aiurat-and-ilya/hv-test-stand/electronics/simulation/hv-test-stand-sim.cir

[Main]
FileType=CIR
Version=12.00
Program=Micro-Cap
Component Version=10.00
Shape Version=11.00
Screen=1920,1080
MCAPVersion=12.2.0.5
Key ID=Demo
NLCnt=221
TXCnt=0

[shapedef]
Name=a_dip8
Block=0,-24,56,40,0,8
BlockLine="Line",-16,-16
BlockLine="Line",-16,0
BlockLine="Line",-16,16
BlockLine="Line",-16,32
BlockLine="Line",72,-16
BlockLine="Line",72,0
BlockLine="Line",72,16
BlockLine="Line",72,32
FColor=None
Line=24,-20,24,-24
Line=32,-20,32,-24
Arc=24,-24,32,-16 , 24,-20,28,-16
Arc=24,-24,32,-16 , 28,-16,32,-20

[shapedef]
Name=Battery
Line=0,0,22,0
Line=22,-3,22,3
Line=26,-7,26,7
Line=26,0,48,0
Current=32,8,16,8

[shapedef]
Name=Capacitor
Line=0,0,22,0
Line=22,-8,22,8
Line=26,-8,26,8
Line=26,0,48,0
Current=32,12,16,12

[shapedef]
Name=Diode
Root="Diode.root",0,0,0

[shapedef]
Name=Diode.root
Line=0,0,20,0
Line=28,0,48,0
Rectangle=18,-8,20,8
PolyClosed=3
PolyLine=20,0
PolyLine=28,-8
PolyLine=28,8
Current=32,16,16,16

[shapedef]
Name=DNMOS
Root="Mos2.root",0,0,0
Line=14,0,24,0
PolyClosed=3
PolyLine=17,0
PolyLine=20,-3
PolyLine=20,3

[shapedef]
Name=DPMOS
Root="Mos2.root",0,0,0
Line=14,0,24,0
PolyClosed=3
PolyLine=17,-3
PolyLine=17,3
PolyLine=20,0

[shapedef]
Name=Ground
Line=0,0,12,0
Line=12,-8,12,8
Line=18,-4,18,4
Line=24,0,24,0

[shapedef]
Name=Inductor
Line=42,0,48,0
Line=0,0,5,0
Arc=5,-7,17,7 , 11,-7,5,0
Arc=13,-7,25,7 , 19,-7,13,0
Arc=29,-7,41,7 , 35,-7,29,0
Arc=21,-7,33,7 , 27,-7,21,0
Arc=6,-7,18,7 , 18,0,12,-7
Arc=14,-7,26,7 , 26,0,20,-7
Arc=22,-7,34,7 , 34,0,28,-7
Arc=30,-7,42,7 , 42,0,36,-7
Line=11,-7,12,-7
Line=19,-7,20,-7
Line=27,-7,28,-7
Line=35,-7,36,-7
Arc=13,-4,17,2 , 13,-1,15,2
Arc=29,-4,33,2 , 29,-1,31,2
Arc=21,-4,25,2 , 21,-1,23,2
Arc=14,-4,18,2 , 16,2,18,-1
Arc=30,-4,34,2 , 32,2,34,-1
Arc=22,-4,26,2 , 24,2,26,-1
Line=15,2,16,2
Line=23,2,24,2
Line=31,2,32,2
Line=5,5,9,5
Line=41,5,41,9
Line=39,7,43,7
Current=32,8,16,8

[shapedef]
Name=Mos2.root
Line=0,8,10,8
Line=10,-8,10,8
Line=14,-11,14,-5
Line=14,-3,14,3
Line=14,5,14,11
Line=14,-8,24,-8
Line=14,8,24,8
Line=24,0,24,24
Line=24,-8,24,-24
Current=32,-24,32,-16
Current=32,24,32,16
Current=0,0,8,0

[shapedef]
Name=Resistor
PolyOpen=12
PolyLine=0,0
PolyLine=0,0
PolyLine=12,0
PolyLine=14,-4
PolyLine=18,4
PolyLine=22,-4
PolyLine=26,4
PolyLine=30,-4
PolyLine=34,4
PolyLine=36,0
PolyLine=48,0
PolyLine=48,0
Current=32,8,16,8

[shapedef]
Name=TL494_L
Rectangle=16,0,128,224
FColor=None
Line=0,16,16,16
Line=0,48,16,48
Line=0,80,16,80
Line=0,112,16,112
Line=0,144,16,144
Line=0,176,16,176
Line=0,208,16,208
Line=128,16,144,16
Line=128,48,144,48
Line=128,80,144,80
Line=128,112,144,112
Line=128,144,144,144
Line=128,176,144,176
Line=128,208,144,208
Line=72,-16,72,0
Line=72,224,72,240
Text="C1"
TextInfo=109,10,125,25 , -11,0,"Arial"
Text="E1"
TextInfo=109,42,125,57 , -11,0,"Arial"
Text="C2"
TextInfo=107,74,123,89 , -11,0,"Arial"
Text="E2"
TextInfo=108,106,124,121 , -11,0,"Arial"
Text="Vcc"
TextInfo=61,7,82,22 , -11,0,"Arial"
Text="GND"
TextInfo=61,206,88,221 , -11,0,"Arial"
Text="REF"
TextInfo=23,203,47,218 , -11,0,"Arial"
Text="OCT"
TextInfo=100,203,126,218 , -11,0,"Arial"
Text="-IN2"
TextInfo=24,169,47,184 , -11,0,"Arial"
Text="+IN2"
TextInfo=22,138,48,153 , -11,0,"Arial"
Text="-IN1"
TextInfo=22,105,45,120 , -11,0,"Arial"
Text="+IN1"
TextInfo=21,74,47,89 , -11,0,"Arial"
Text="FB"
TextInfo=23,42,39,57 , -11,0,"Arial"
Text="DTC"
TextInfo=23,10,48,25 , -11,0,"Arial"
Text="R"
TextInfo=112,138,122,153 , -11,0,"Arial"
Text="C"
TextInfo=112,171,122,186 , -11,0,"Arial"

[shapedef]
Name=C_gost
Line=0,0,22,0
Line=22,-8,22,8
Line=25,-8,25,8
Line=25,0,48,0
Current=32,12,16,12

[shapedef]
Name=E_gost
Line=0,0,12,0
Line=36,0,48,0
Current=32,16,16,16
Ellipse=12,-12,36,12
FColor=None
Line=16,0,32,0
Line=32,0,24,-2
Line=32,0,24,2

[shapedef]
Name=Ground_GOST
Line=1,0,13,0
Line=13,-8,13,8

[shapedef]
Name=L_gost
Current=31,8,15,8
Arc=5,-6,15,5 , 19,0,3,0
Ellipse=44,-6,47,-3
Line=48,0,42,0
Line=5,0,0,0
Arc=14,-6,24,5 , 28,0,12,0
Arc=23,-6,33,5 , 37,0,21,0
Arc=32,-6,42,5 , 46,0,30,0

[shapedef]
Name=R_gost
Current=32,8,16,8
Rectangle=14,-4,34,4
FColor=None
Line=0,0,14,0
Line=34,0,48,0

[shapedef]
Name=VD_gost
Line=0,0,48,0
Current=32,16,16,16
PolyClosed=3
PolyLine=20,0
PolyLine=30,-6
PolyLine=30,6
FColor=None
Line=20,-6,20,6

[compdef]
Name=Battery
Definition=Battery
Shape=Battery
Mask=6913
Used=52
memo=Battery
Label Offset=19,7,10,13
PinCnt=2
Pin="Plus",6,0,-4,-5
Pin="Minus",0,0,-10,-5

[compdef]
Name=Ground
Definition=Ground
Shape=Ground
Mask=1793
Used=278
memo=Ground
Label Offset=0,0,0,0
PinCnt=1
Pin="PinA",0,0,-3,-7

[compdef]
Name=TL494
Definition=Macro
Shape=TL494_L
Mask=4224
Used=1
memo=Pulse Width Modulation Control Circuit
Label Offset=91,228,4,90
PinCnt=16
Pin="DTC",a,0,2,-11,-3
Pin="FB",a,0,6,-6,-4
Pin="IN1",a,0,10,-6,-3
Pin="-IN1",a,0,14,-9,-4
Pin="IN2",a,0,18,-7,-4
Pin="-IN2",a,0,22,-10,-4
Pin="Vref",a,0,26,-7,-4
Pin="CT1",a,18,2,-8,-3
Pin="ET1",a,18,6,-7,-3
Pin="CT2",a,18,10,-9,-1
Pin="ET2",a,18,14,-7,-2
Pin="Rt",a,18,18,-6,-3
Pin="Ct",a,18,22,-5,-3
Pin="OCT",a,18,26,-9,-3
Pin="Vcc",a,9,-2,2,0
Pin="GND",a,9,30,2,-1

[compdef]
Name=Resistor
Definition=Resistor
Shape=Resistor
Mask=6913
Used=166
memo=Resistor
Label Offset=18,6,8,11
PinCnt=2
Pin="Plus",6,0,-10,-4
Pin="Minus",0,0,-14,-4

[compdef]
Name=Capacitor
Definition=Capacitor
Shape=Capacitor
Mask=7937
Used=31
memo=Capacitor
Label Offset=16,12,12,12
PinCnt=2
Pin="Plus",6,0,5,5
Pin="Minus",0,0,-30,7

[compdef]
Name=Inductor
Definition=Inductor
Shape=Inductor
Mask=7681
Used=37
memo=Inductor
Label Offset=18,9,11,12
PinCnt=2
Pin="Plus",6,0,-5,-9
Pin="Minus",0,0,-3,-9

[compdef]
Name=Diode
Definition=Diode
Shape=Diode
Mask=5377
Used=10
memo=Diode
Label Offset=17,10,12,12
PinCnt=2
Pin="Anode",6,0,-9,-8
Pin="Cathode",0,0,-20,-8

[compdef]
Name=IR2302
Definition=Subckt
Shape=a_dip8
Mask=20608
memo=Half-Bridge Driver
Label Offset=18,40,26,12
PinCnt=8
Pin="Vcc",a,-2,-2,19,7
Pin="IN",a,-2,0,19,7
Pin="SD",a,-2,2,19,7
Pin="COM",a,-2,4,19,7
Pin="Vb",a,9,-2,-31,7
Pin="HO",a,9,0,-33,7
Pin="Vs",a,9,2,-31,7
Pin="LO",a,9,4,-32,7

[compdef]
Name=IRF640NS
Definition=Subckt
Shape=DNMOS
Mask=4224
Used=3
memo=N-Channel Power MOSFET Vdss=200V Id=18A Rds=.15ohm
Label Offset=30,-9,-5,27
PinCnt=3
Pin="2",a,0,1,-6,-3
Pin="1",a,3,-3,6,6
Pin="3",a,3,3,6,6

[compdef]
Name=MURS320
Definition=Diode
Shape=Diode
Mask=6016
memo=Super Fast Rectifier Vr=200V Io=3A
Link=http://www.diodes.com/datasheets/ds30197.pdf
Label Offset=17,10,12,12
PinCnt=2
Pin="Anode",6,0,-9,-8
Pin="Cathode",0,0,-20,-8

[compdef]
Name=IRF6215_IR
Definition=Subckt
Shape=DPMOS
Mask=4224
memo=P-Channel HEXFET Power MOSFET 150V 13A
Label Offset=30,-13,-6,26
PinCnt=3
Pin="1",a,3,-3,5,5
Pin="2",a,0,1,-3,-3
Pin="3",a,3,3,6,6

[Circuit]
Window Placement=2,3, -1,-1, -8,-31, 35,0,1357,557
Default Object=Color=#000080
Default Object Font=Height=-15,FStyle=0,Color=#000080,Name=Arial
Default Object Apply Border To Text=No
Default Object Apply Fill To Text=No
Default Object GridSnap=No
NodeVoltageFormat=3
CurrentFormat=3
PowerFormat=3
PathDelayFormat=3
WarningFormat=3
GridTextFormulaFormat=3
Window Placement in Transient Analysis=2,3, -1,-1, -8,-31, 104,104,1738,679
Window Placement in Transient Probe=0,1, -1,-1, -8,-31, 958,0,1916,857
Window Placement in AC Analysis=2,3, -1,-1, -8,-31, 104,104,1738,679
SpiceType=AMBIGUOUS
Title_Block_Border=None
Title_Block=False
Show Nodes=False
Show Voltages=True
Show Current=False
Show Power=False
Show Condition=False
Show Pin Connections=False
Show Connection Warnings=False
Show Cross=False
Show Attribute Text=True
Show Grid Text=True

[Comp]
Name=Battery
Px=512,232
Rot=3

[Attr]
ON=-30,-40,PART
V=V1
Style=8192

[Attr]
ON=-29,-30,VALUE
V=12
Style=8192

[Attr]
ON=0,0,PACKAGE
V

[Comp]
Name=Ground
Px=512,280
Rot=7

[Comp]
Name=TL494
Px=568,416

[Attr]
ON=93,-31,PART
V=X1
Style=8192

[Attr]
ON=83,-17,FILE
V=TL494
Style=8192

[Attr]
ON=91,270,PACKAGE
V=SOIC16

[Comp]
Name=Resistor
Px=800,600
Rot=1

[Attr]
ON=-20,12,PART
V=R1
Style=8192

[Attr]
ON=-30,23,RESISTANCE
V=11k
Style=8192

[Attr]
ON=0,0,PACKAGE
V

[Wire]
Pxs=712,560,800,560

[Wire]
Pxs=800,560,800,600

[Comp]
Name=Ground
Px=800,664
Rot=7

[Wire]
Pxs=800,648,800,664

[Comp]
Name=Capacitor
Px=752,648
Rot=3

[Attr]
ON=-28,-37,PART
V=C1
Style=8192

[Attr]
ON=-27,-26,CAPACITANCE
V=1n
Style=8192

[Attr]
ON=0,0,PACKAGE
V

[Wire]
Pxs=712,592,752,592

[Wire]
Pxs=752,592,752,600

[Comp]
Name=Ground
Px=752,664
Rot=7

[Wire]
Pxs=752,648,752,664

[Comp]
Name=Ground
Px=640,664
Rot=7

[Wire]
Pxs=640,656,640,664

[Comp]
Name=Resistor
Px=360,632
Rot=1

[Attr]
ON=-23,12,PART
V=R4
Style=8192

[Attr]
ON=-28,23,RESISTANCE
V=10k
Style=8192

[Attr]
ON=0,0,PACKAGE
V

[Comp]
Name=Resistor
Px=360,696
Rot=1

[Attr]
ON=-23,9,PART
V=R5
Style=8192

[Attr]
ON=-23,21,RESISTANCE
V=1k
Style=8192

[Attr]
ON=0,0,PACKAGE
V

[Comp]
Name=Ground
Px=360,752
Rot=7

[Comp]
Name=Capacitor
Px=392,680
Rot=3

[Attr]
ON=-25,-38,PART
V=C2
Style=8192

[Attr]
ON=-22,-25,CAPACITANCE
V=1u
Style=8192

[Attr]
ON=0,0,PACKAGE
V

[Comp]
Name=Ground
Px=1352,688
Rot=7

[Comp]
Name=Inductor
Px=1136,312
Rot=6

[Attr]
ON=-34,-31,PART
V=L1
Style=8192

[Attr]
ON=-39,-20,INDUCTANCE
V=220u
Style=8192

[Attr]
ON=0,0,PACKAGE
V

[Wire]
Pxs=1248,312,1256,312

[Comp]
Name=Capacitor
Px=1256,392
Rot=3

[Attr]
ON=13,-37,PART
V=C4
Style=8192

[Attr]
ON=13,-25,CAPACITANCE
V=47u
Style=8192

[Attr]
ON=0,0,PACKAGE
V

[Wire]
Pxs=1256,312,1256,344

[Comp]
Name=Ground
Px=1256,408
Rot=7

[Wire]
Pxs=1256,392,1256,408

[Comp]
Name=Capacitor
Px=1304,392
Rot=3

[Attr]
ON=13,-37,PART
V=C5
Style=8192

[Attr]
ON=13,-25,CAPACITANCE
V=10n
Style=8192

[Attr]
ON=0,0,PACKAGE
V

[Wire]
Pxs=1256,312,1304,312

[Wire]
Pxs=1304,312,1304,344

[Comp]
Name=Ground
Px=1304,408
Rot=7

[Wire]
Pxs=1304,392,1304,408

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
V=100
Style=8192

[Attr]
ON=0,0,PACKAGE
V

[Wire]
Pxs=640,368,640,384

[Comp]
Name=Capacitor
Px=560,384
Rot=4

[Attr]
ON=14,-36,PART
V=C12
Style=8192

[Attr]
ON=13,-23,CAPACITANCE
V=100n
Style=8192

[Attr]
ON=0,0,PACKAGE
V

[Wire]
Pxs=608,384,640,384

[Wire]
Pxs=640,384,640,400

[Comp]
Name=Ground
Px=544,384
Rot=2

[Wire]
Pxs=544,384,560,384

[Comp]
Name=Resistor
Px=1192,624
Rot=1

[Attr]
ON=-29,11,PART
V=R56
Style=8192

[Attr]
ON=-27,23,RESISTANCE
V=1.5
Style=8192

[Attr]
ON=0,0,PACKAGE
V

[Wire]
Pxs=1192,672,1192,688

[Wire]
Pxs=1192,592,1192,624

[Comp]
Name=MURS320
Px=1248,312
Rot=2

[Attr]
ON=-32,-35,PART
V=D7
Style=8192

[Attr]
ON=-50,-24,MODEL
V=MURS320
Style=8192

[Attr]
ON=-44,-66,PACKAGE
V=SMC

[Comp]
Name=MURS320
Px=1032,320
Rot=7

[Attr]
ON=-29,12,PART
V=D8
Style=8192

[Attr]
ON=-66,24,MODEL
V=MURS320
Style=8192

[Attr]
ON=-39,54,PACKAGE
V=SMC

[Wire]
Pxs=1032,312,1088,312

[Wire]
Pxs=744,152,744,312

[Comp]
Name=Diode
Px=912,384
Rot=5

[Attr]
ON=-34,-37,PART
V=D10
Style=8192

[Attr]
ON=-55,-23,MODEL
V=UF4007
Style=8192

[Attr]
ON=12,-68,PACKAGE
V=DO-41

[Comp]
Name=Resistor
Px=912,440
Rot=5

[Attr]
ON=-31,-34,PART
V=R57
Style=8192

[Attr]
ON=-30,-23,RESISTANCE
V=100
Style=8192

[Attr]
ON=0,0,PACKAGE
V

[Wire]
Pxs=912,440,912,464

[Wire]
Pxs=912,384,912,392

[Wire]
Pxs=912,312,912,336

[Wire]
Pxs=912,312,1032,312

[Comp]
Name=Capacitor
Px=848,624
Rot=5

[Attr]
ON=10,-34,PART
V=C13
Style=8192

[Attr]
ON=9,-22,CAPACITANCE
V=100n
Style=8192

[Attr]
ON=0,0,PACKAGE
V

[Wire]
Pxs=848,512,848,576

[Wire]
Pxs=848,512,912,512

[Comp]
Name=Ground
Px=848,664
Rot=7

[Wire]
Pxs=848,624,848,664

[Comp]
Name=Diode
Px=744,368
Rot=5

[Attr]
ON=9,-37,PART
V=D11
Style=8192

[Attr]
ON=10,-25,MODEL
V=UF4007
Style=8192

[Attr]
ON=12,-68,PACKAGE
V=DO-41

[Wire]
Pxs=744,368,744,376

[Wire]
Pxs=744,312,744,320

[Comp]
Name=Diode
Px=1288,592
Rot=4

[Attr]
ON=10,-34,PART
V=D12
Style=8192

[Attr]
ON=0,-20,MODEL
V=UF4007
Style=8192

[Attr]
ON=17,-66,PACKAGE
V=DO-41

[Wire]
Pxs=1272,592,1288,592

[Wire]
Pxs=1336,592,1352,592

[Wire]
Pxs=1352,592,1352,624

[Wire]
Pxs=688,152,744,152

[Wire]
Pxs=544,152,544,312

[Wire]
Pxs=544,152,576,152

[Comp]
Name=Capacitor
Px=1216,520
Rot=3

[Attr]
ON=13,-37,PART
V=C14
Style=8192

[Attr]
ON=13,-25,CAPACITANCE
V=450p
Style=8192

[Attr]
ON=0,0,PACKAGE
V

[Comp]
Name=Resistor
Px=1216,472
Rot=3

[Attr]
ON=7,-43,PART
V=R58
Style=8192

[Attr]
ON=6,-31,RESISTANCE
V=4.1k
Style=8192

[Attr]
ON=0,0,PACKAGE
V

[Wire]
Pxs=1192,416,1216,416

[Wire]
Pxs=640,312,640,320

[Wire]
Pxs=544,312,640,312

[Comp]
Name=IRF6215_IR
Px=664,176
Rot=5

[Attr]
ON=-10,-54,PART
V=X11
Style=8192

[Attr]
ON=-34,-39,NAME
V=IRF6215_IR
Style=8192

[Attr]
ON=-6,-82,PACKAGE
V=TO-220AB

[Wire]
Pxs=656,176,656,216

[Wire]
Pxs=1216,520,1216,528

[Wire]
Pxs=1192,528,1216,528

[Wire]
Pxs=1192,528,1192,592

[Wire]
Pxs=1192,416,1192,464

[Wire]
Pxs=1216,416,1216,424

[Wire]
Pxs=1080,544,1080,592

[Wire]
Pxs=1080,592,1160,592

[Schematic]
CurrentSection 0=0
CurrentSection 1=0
CurrentSection 2=0
CurrentSection 3=0
Splitter.xs=0
Splitter.ys=0
TextQuad=4099
Scale=1
GridUser=10
ShapeGroups="GOST","Main","Euro","Polarity","Main1","Electrolytic","GroundArrow","DeMorgan","Main2","Electrolytic_GOST","Main111"
CalcRMS=False
CalcAVG=False
CalcPeak=False
CalcVoltage=True
DisplayMeasure=Last
ShareScales=True

[Tools]
Pos=Top
FILESAVEASOLD=No
BOM=No
FILEPCB=No
PROBE=Yes
SELECT=Yes
PAN=Yes
COMP=Yes
TEXT=Yes
WIRE=Yes
WIRED=Yes
BUS=Yes
GRAPHIC=Yes
FLOWCHART=Yes
LINE=No
ELLIPSE=No
RECT=No
DIAM=No
ARC=No
PIE=No
TRIANGLE=No
STAR=No
LEFTBRK=No
RIGHTBRK=No
BOTHBRK=No
META=Yes
PARALLELOGRAM=No
FC_PROCESS=No
FC_ALT_PROCESS=No
FC_DECISION=No
FC_DATA=No
FC_PREDEFPROCESS=No
FC_INTERNALSTORAGE=No
FC_DOCUMENT=No
FC_MULTIDOCUMENT=No
FC_TERMINATOR=No
FC_PREPARATION=No
FC_MANUALINPUT=No
FC_MANUALOPERATION=No
FC_CONNECTOR=No
FC_OFFPAGECONNECTOR=No
FC_PUNCHCARD=No
FC_PUNCHEDTAPE=No
FC_SUMMING_JUNCTION=No
FC_OR=No
FC_COLLATE=No
FC_SORT=No
FC_EXTRACT=No
FC_MERGE=No
FC_STORED_DATA=No
FC_DELAY=No
FC_SAS=No
FC_MAGNETIC_DISK=No
FC_DAS=No
FC_DISPLAY=No
SPREAD_SHEET=Yes
POLYCLOS=No
POLYOPEN=No
FLAG=Yes
INFO=Yes
HELP=Yes
HELP_SPICE=No
LINK=Yes
CHECK=Yes
REGION_ENABLE=Yes
TITLE_BLOCK=Yes
DIGTRC=No
DIGTRC2=No
BUILD_COMMAND=Yes
DIGALL=No
GRIDTEXT=Yes
COMPTEXT=Yes
NODE=Yes
MEASURED=Yes
NODEV=Yes
CURRENT=Yes
POWER=Yes
CONDITIN=Yes
PIN=Yes
CONNWARN=Yes
CROSS=Yes
GRID=Yes
BORDER=Yes
BORDERONE=Yes
TITLE=Yes
RUBBER=Yes
PROPERTY=Yes
STEP=Yes
MIRROR=Yes
ROTATE=Yes
FLIPY=Yes
FLIPX=Yes
CIR_MAKEMACRO=No
CLEARCUTWIRE=No
CLIPBOARDCIRPAGE2BMM=No
FINDCOMP=Yes
FIND=Yes
REPEAT=No
REPLACE=No
MODEL=Yes
CIR2CKT=Yes
ATTDISP=Yes
ENABLE=Yes
DISABLE=Yes
ENABLE_WITH=Yes
TOFRONT=Yes
TOBACK=Yes
SELNEXT=Yes
PAGEADD=Yes
PAGEADDTEXT=No
ADDSECTION=No
PAGEDEL=Yes
ZOOMIN=Yes
ZOOMOUT=Yes
AUTOSCALECIR=Yes
GOTOFLAG=Yes
UPLEVEL=Yes
COLOR=Yes
FONT=Yes
STYLE=Yes
DM_LAST=No
DM_RMS=No
DM_AVG=No
DM_PEAK=No
GRID_NONE=No
GRID_NORMAL=No
GRID_BOLD_5=No
GRID_BOLD_6=No
GRID_BOLD_USER=No
GRAPH_PAPER=No
SPLITCIRTEXTH=No
SPLITCIRTEXTV=No
SPACE_SPLITTERS_EVENLY=No
NORMALCIR=No
RENAMEDEFINE=No
RENAMECMP=No
ATTALIGN=No
RESETNODEPOS=No
FIT2STANDARD=No
NODESNAP=No
MOVETEXT=No
TEXTINC=No
TOGGLETEXT=No
TOGGLEMODE=No
TOLERANCE=No
ALIGNAB=No
ALIGNLEFT=Yes
ALIGNCENTER=Yes
ALIGNRIGHT=Yes
ALIGNTOP=Yes
ALIGNMIDDLES=Yes
ALIGNBOTTOM=Yes

[Section]
Index=0
Name="схема"
Type=Main
Enable=True
CurrentPage 0=0
CurrentPage 1=0
CurrentPage 2=0
CurrentPage 3=0
TabSize 0=425
TabSize 1=425
TabSize 2=425
TabSize 3=425

[Page]
Index=0
Section=0
Print=True
Enable=True
Name=Main
PrinterScale=1
Scale 0=1
Scale 1=1
Scale 2=1
SB 3=217,254
Scale 3=1
Px=1002,646
WinBackGround Color=#FFFFFF
Select Color=#FF0000
Anchor Color=#000000
Select Box Color=#000080
Grid Text Color=Height=-12,FStyle=0,Color=#0000FF,Name=Verdana
Grid Text RTF=False
Grid Text Angle=0
Grid Text GridSnap=True
Grid Text PinIt=False
Grid Text JustifyH=Left
Grid Text JustifyV=Bottom
Grid GradientColor2=None
Grid OutlineThickness=1
Grid OutlineColor=None
Component Color=#0000FF
Attribute Text=Height=-12,FStyle=0,Color=#008000,Name=Verdana
Wire Color=#008000
Bus Color=#008000
Pin Connection=Height=-10,FStyle=0,Color=#FF0000,Name=Arial
Pin Marker Color=#008000
Node Number=Height=-11,FStyle=0,Color=#FF00FF,Name=Arial
Node Voltage Color=Height=-11,FStyle=0,Color=#000000,Name=Arial
Dynamic AC Voltage Color=#E4E4E4
Text Banner Text=Height=-15,FStyle=0,Color=#800000,Name=Arial
Title Block Background=#C0C0C0
Current=Height=-11,FStyle=0,Color=#0000FF,Name=Arial
Power/Condition=Height=-11,FStyle=0,Color=#FF0000,Name=Arial
Digital Path Color=#FF0000
Title Block Border=#000000
Disabled	Color=#C0C0C0
Search Color=#FFFF00
Grid Color=#000000
Graph Paper=#E4E4E4
Digital 0 Color=#000000
Digital R Color=#FFFF00
Digital F Color=#FFFF00
Digital 1 Color=#FF0000
Digital X Color=#C0C0C0
Digital Z Color=#808080
Block Select Color=#51F998

[Page]
Index=1
Section=0
Type=Text
Print=False
Enable=True
Name=Text
SB 0=0,2
Font=Height=-15,FStyle=0,Color=#000000,Name=Courier New
Comment Color=#008000
WinBackGround Color=#FFFFFF
Disabled	Color=#C0C0C0
KeyWord Color=#0000FF
Error	Color=#FF0000
Search Color=#FFFF00

[Page]
Index=2
Section=0
Type=Text
Print=False
Enable=True
Name=Models
SB 0=0,159
Font=Height=-15,FStyle=0,Color=#000000,Name=Courier New
Comment Color=#008000
WinBackGround Color=#FFFFFF
Disabled	Color=#C0C0C0
KeyWord Color=#0000FF
Error	Color=#FF0000
Search Color=#FFFF00

[Page]
Index=3
Section=0
Type=Info
Print=False
Enable=True
Name=Info
Font=Height=-15,FStyle=0,Color=#000000,Name=Courier New
Comment Color=#008000
WinBackGround Color=#FFFFFF
Disabled	Color=#C0C0C0
KeyWord Color=#0000FF
Error	Color=#FF0000
Search Color=#FFFF00

[Text Area]
Section=0
Page=1
Text=.OPTIONS ITL1=250
Text=.OPTIONS PIVREL=1
Text=.OPTIONS ITL4=50
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
